badrbouslikhin/Enchante/Board shape/stl2dxf.scad

projection(cut=false) import("/Volumes/C/Users/Badr/Desktop/EE/YAPCBBC/Board shape
/board_shape.stl");
